SteveJO789/BPMWATCH/firmware/slave/src/BatteryMonitor.cpp

#include "BatteryMonitor.h"

void BatteryMonitor::begin() {
  // TODO: Configure ADC pin and voltage divider.
}

int BatteryMonitor::readPercent() {
  // TODO: Convert calibrated ADC voltage to percent.
  return 95;
}
